sander110419/openglasshole/hardware/cad/stl/fit_coupon.stl

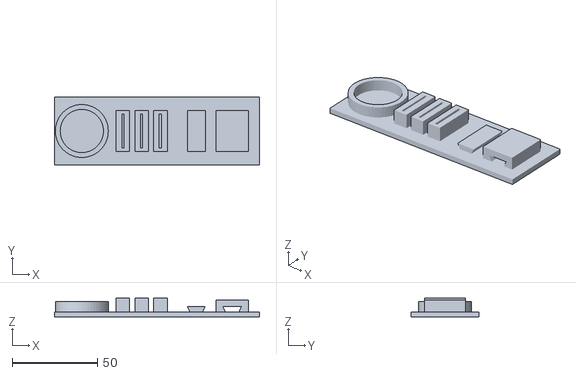
[picture p16: CAD file, 2026-07-17]
hardware/cad/stl/fit_coupon.stl
120.0 x 40.0 x 11.0
