sander110419/openglasshole/hardware/cad/stl/focus_bench_jig.stl

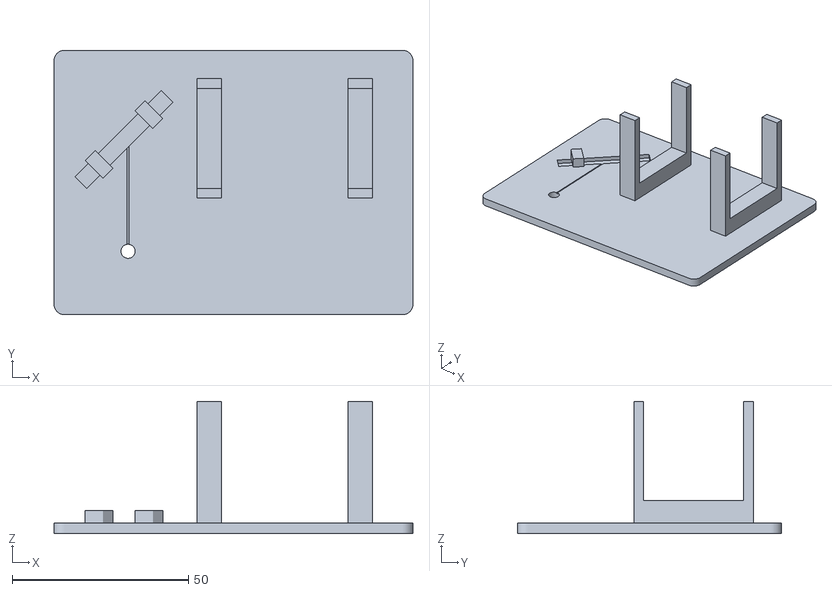
[picture p17: CAD file, 2026-07-17]
hardware/cad/stl/focus_bench_jig.stl
101.8 x 75.0 x 37.5
