sander110419/openglasshole/hardware/cad/stl/cut_template_print.stl

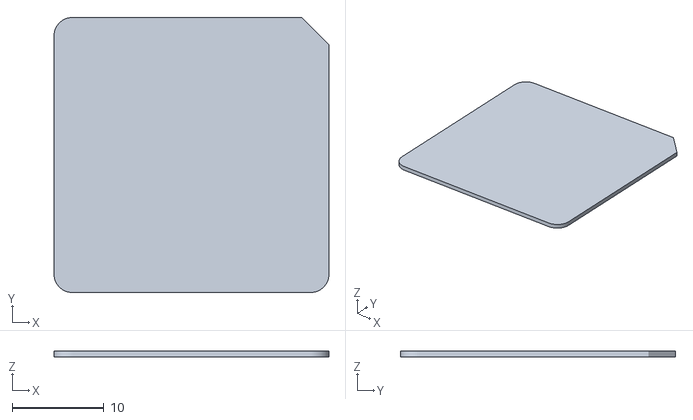
[picture p18: CAD file, 2026-07-17]
hardware/cad/stl/cut_template_print.stl
30.0 x 30.0 x 0.6
