sander110419/openglasshole/hardware/cad/stl/rear_pod.stl

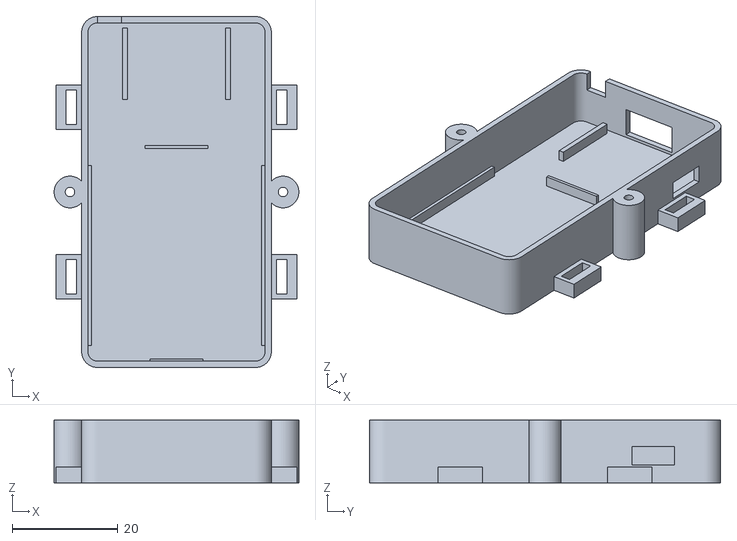
[picture p19: CAD file, 2026-07-17]
hardware/cad/stl/rear_pod.stl
46.3 x 66.4 x 11.9
