sander110419/openglasshole/hardware/cad/stl/combiner_clamp.stl

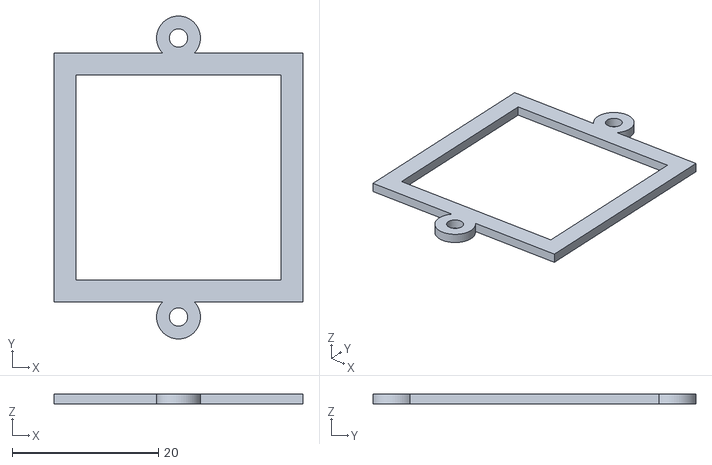
[picture p20: CAD file, 2026-07-17]
hardware/cad/stl/combiner_clamp.stl
34.0 x 44.1 x 1.40
